creid89/PSU_Capstone_Project_2025_BMS/Schematics/BMS Schematics KiCAD/Battery Management System/untitled.kicad_sch

## KiCad design Schematics/BMS Schematics KiCAD/Battery Management System/untitled.kicad_sch (2025-04-21)

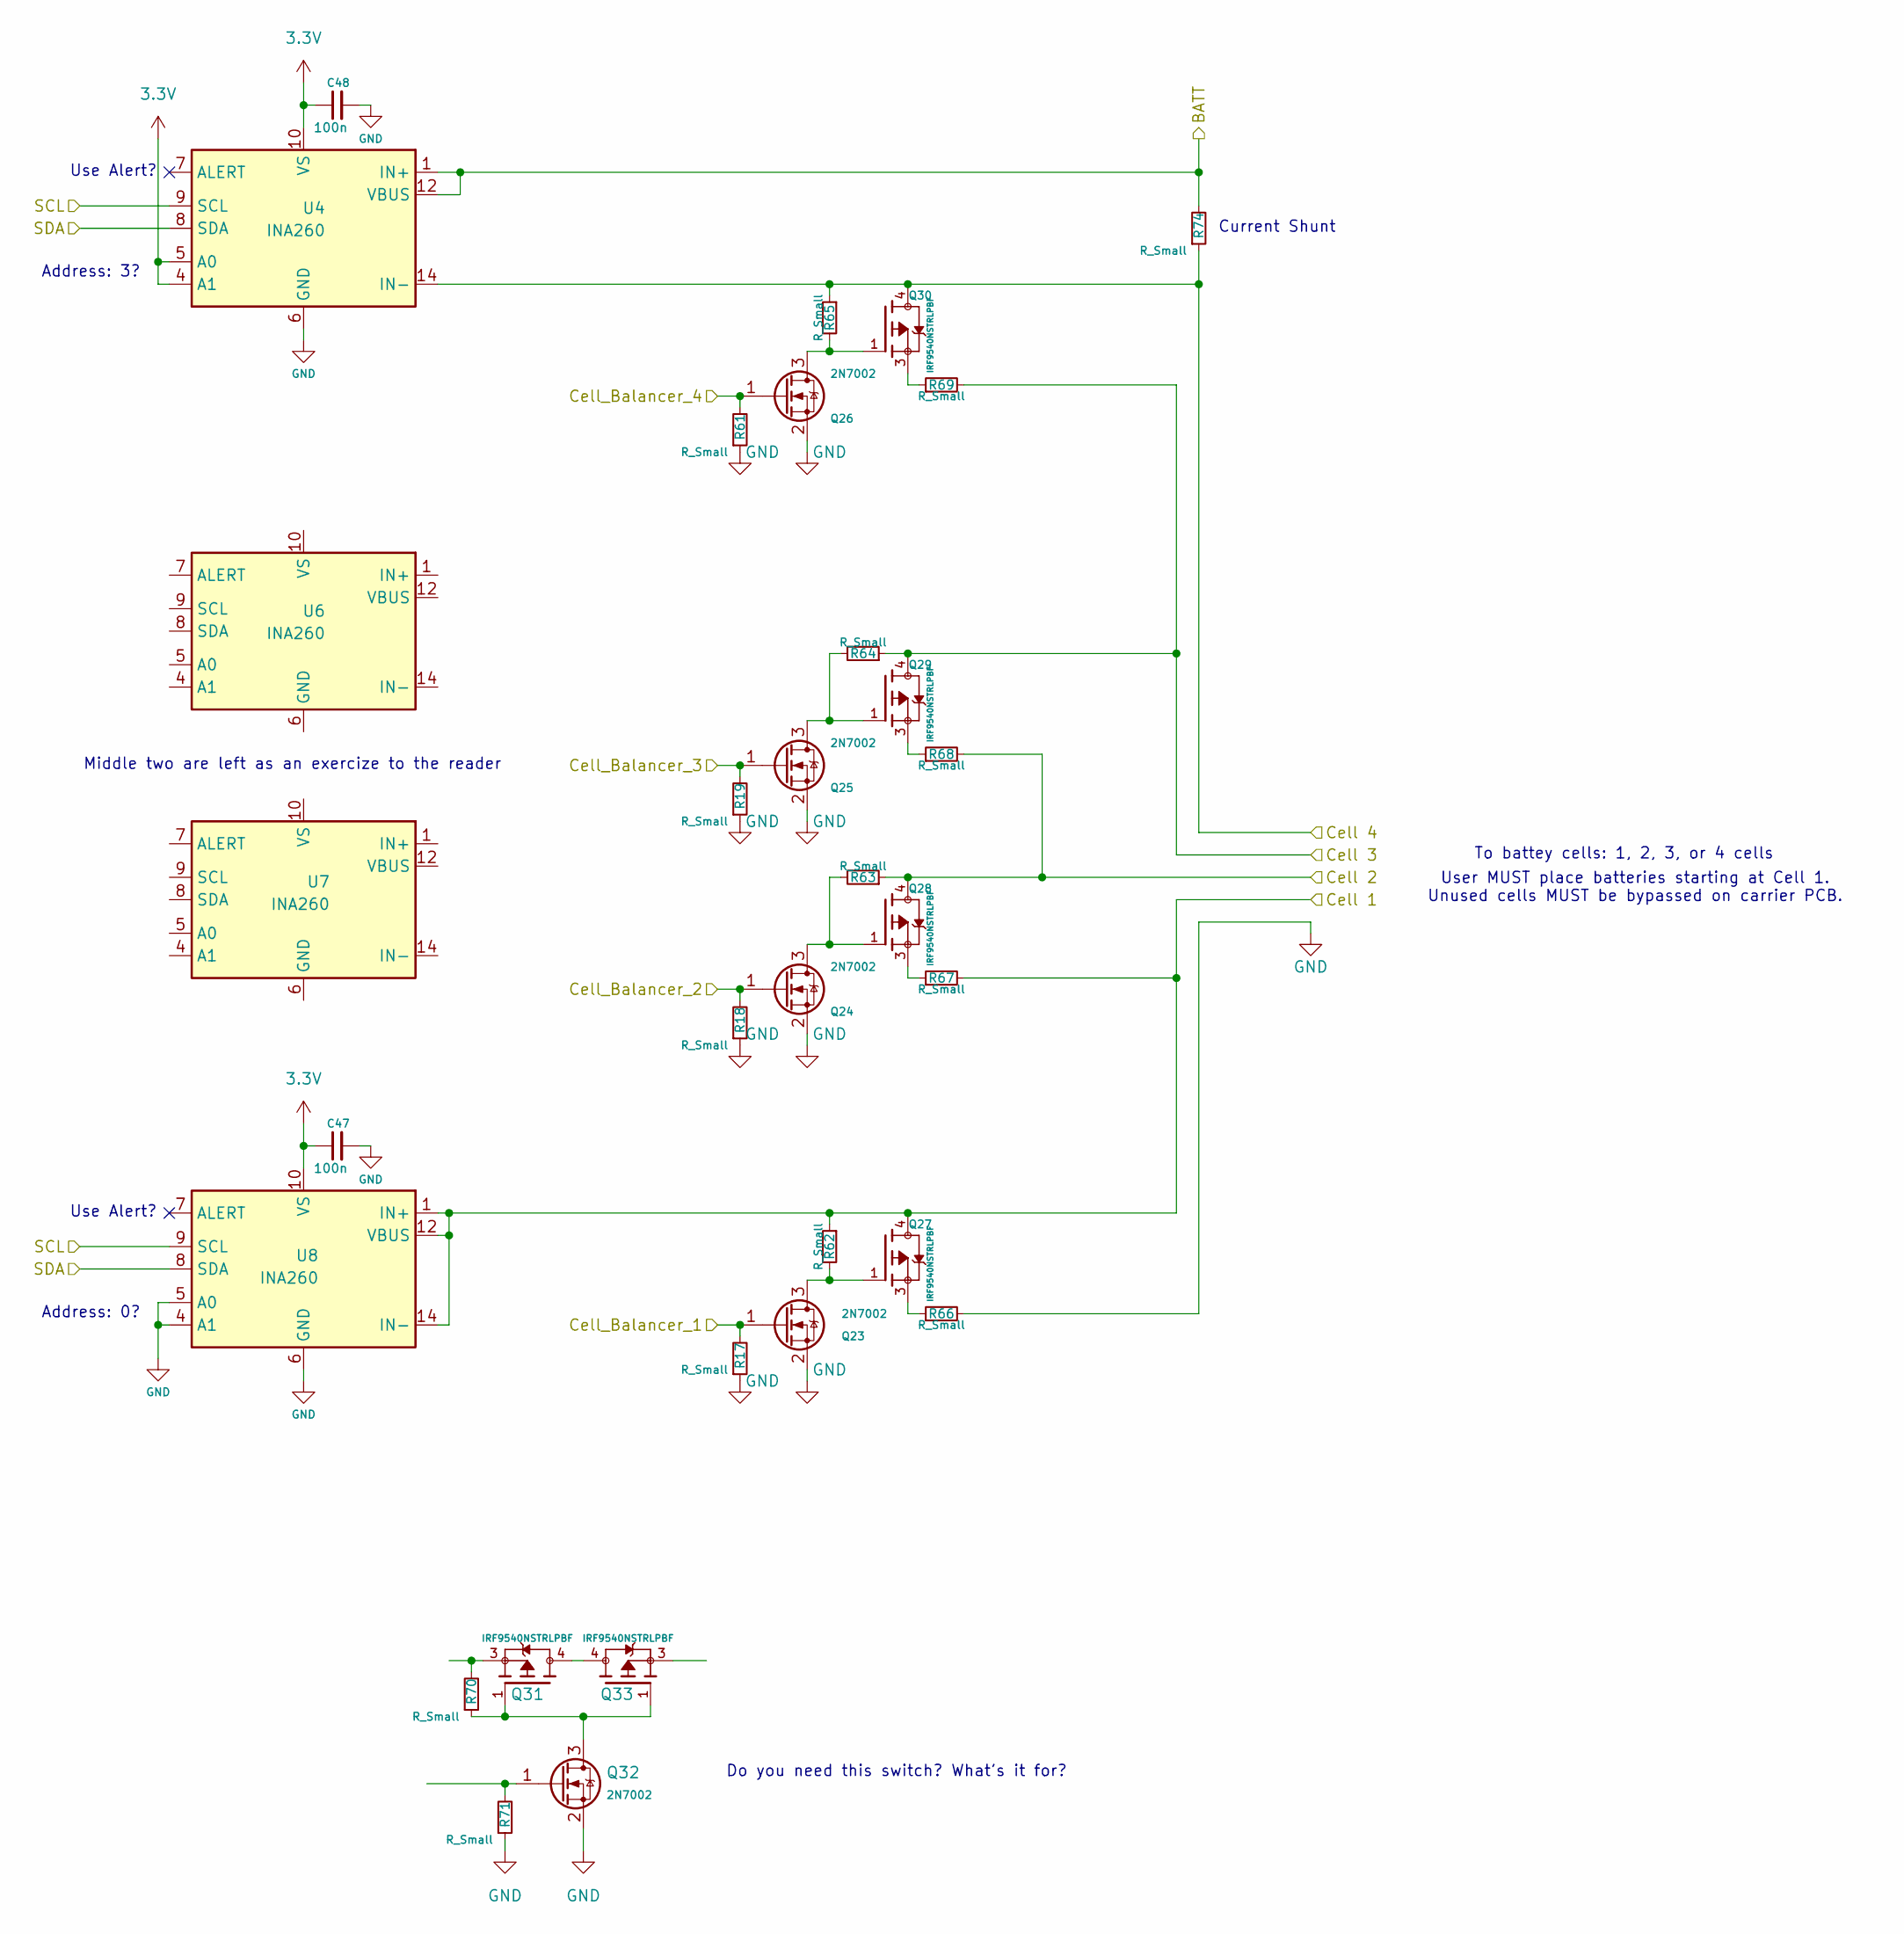
[picture p17: schematic untitled.kicad_sch]

Parts:
C47, C48: 100n; C_0201_0603Metric
Q23, Q24, Q25, Q26, Q32: 2N7002; SOT-23
Q27, Q28, Q29, Q30, Q31, Q33: IRF9540NSTRLPBF; DPAK254P1524X483-4_3N; PARTREV 09/30/05
R17, R18, R19, R61, R71, R74: R_Small; R_0201_0603Metric
R62, R63, R64, R65, R66, R67, R68, R69, R70: R_Small
U4, U6, U7, U8: INA260; TSSOP-16_4.4x5mm_P0.65mm

Connections:
3.3V: C47.1, C48.1, U4.4 (A1), U4.5 (A0), U4.10 (VS), U8.10 (VS)
BATT: R74.2, U4.1 (IN+), U4.12 (VBUS)
Cell 1: Q27.4, R62.1, R67.2, U8.1 (IN+), U8.12 (VBUS), U8.14 (IN-)
Cell 2: Q28.4, R63.1, R68.2
Cell 3: Q29.4, R64.1, R69.2
Cell 4: Q30.4, R65.1, R74.1, U4.14 (IN-)
Cell_Balancer_1: Q23.1 (G), R17.2
Cell_Balancer_2: Q24.1 (G), R18.2
Cell_Balancer_3: Q25.1 (G), R19.2
Cell_Balancer_4: Q26.1 (G), R61.2
GND: C47.2, C48.2, Q23.2 (S), Q24.2 (S), Q25.2 (S), Q26.2 (S), Q32.2 (S), R17.1, R18.1, R19.1, R61.1, R66.2, R71.1, U4.6 (GND), U8.4 (A1), U8.5 (A0), U8.6 (GND)
unnamed: Q23.3 (D), Q27.1, R62.2
unnamed: Q24.3 (D), Q28.1, R63.2
unnamed: Q25.3 (D), Q29.1, R64.2
unnamed: Q26.3 (D), Q30.1, R65.2
unnamed: Q27.3, R66.1
unnamed: Q28.3, R67.1
unnamed: Q29.3, R68.1
unnamed: Q30.3, R69.1
unnamed: Q31.1, Q32.3 (D), Q33.1, R70.1
unnamed: Q31.3, R70.2
unnamed: Q31.4, Q33.4
unnamed: Q32.1 (G), R71.2
SCL: U4.9 (SCL), U8.9 (SCL)
SDA: U4.8 (SDA), U8.8 (SDA)

Notes on the sheet:
Address: 0?
Use Alert?
To battey cells: 1, 2, 3, or 4 cells
Current Shunt
Do you need this switch? What's it for?
Address: 3?
User MUST place batteries starting at Cell 1. Unused cells MUST be bypassed on carrier PCB.
Middle two are left as an exercize to the reader
