creid89/PSU_Capstone_Project_2025_BMS/Code/Arduino Library/examples/ESP32_BMS_Controller_Library_Test_v2/ESP32_BMS_Controller_Library_Test_v2.ino

#include <BMSController.h>

//Using Huzzah Adafruit ESP32
//#define SDA_PIN 23
//#define SCL_PIN 22
#define BMS_ADDR 0x58

BMSController BMS(BMS_ADDR);

void setup() {
  Serial.begin(115200);

  while (!BMS.begin()) {
    Serial.println();
    Serial.println("Waiting for BMS to respond...");
    delay(2000);
  }
  Serial.println("——————————————————————");
  Serial.println("          BMS connected!");
  Serial.println("——————————————————————");
  delay(500);

  BMS.setChargeVoltage(16.8);       // command 0x10
  delay(100);
  BMS.setVsysMin(8.0);              // command 0x11
  delay(100);
  BMS.setInputVoltageLimit(12.5);   // command 0x13
  delay(100);
  BMS.setChargeCurrent(1.5);        // command 0x14
  delay(100);
  BMS.setInputCurrentLimit(3000.0);   // command 0x15
  delay(100);
  BMS.setCellMaxCutOffV(4.0);        // command 0x16
  delay(100);
  BMS.setCellMinCutOffV(2.0);        // command 0x17
  delay(100);
  BMS.setPack_stock_capacity(5200.0);   // command 0x18 

  //BMS.FinishedConfiguration(true);  //command 0x19
  Serial.println("——————————————————————");
  Serial.println("          BMS Configured!");
  Serial.println("——————————————————————");
}

void loop() {
  delay(1500);
  float chargeCurrent = BMS.getChargeCurrent();
  Serial.print("Charge Current: ");
  Serial.println(chargeCurrent, 3);
   delay(1500);
  float cellVoltage1 = BMS.getCell1Voltage();
  Serial.print("Cell 1 Voltage: ");
  Serial.println(cellVoltage1 , 3);
  delay(1500);
  float cellVoltage2 = BMS.getCell2Voltage();
  Serial.print("Cell 2 Voltage: ");
  Serial.println(cellVoltage2 , 3);
  delay(1500);
  float cellVoltage3 = BMS.getCell3Voltage();
  Serial.print("Cell 3 Voltage: ");
  Serial.println(cellVoltage3 , 3);
  delay(1500);
  float cellVoltage4 = BMS.getCell4Voltage();
  Serial.print("Cell 4 Voltage: ");
  Serial.println(cellVoltage4 , 3);
  delay(1500);
  float totalPackVoltage = BMS.getTotalPackVoltage();
  Serial.print("Total Pack Voltage: ");
  Serial.println(totalPackVoltage , 3);
  delay(1500);
  float SoC = BMS.getSoC();
  Serial.print("SoC: ");
  Serial.println(SoC , 3);
  delay(1500);
  float PercentSoC = BMS.getPercentSoC();
  Serial.print("Percent SoC: ");
  Serial.print(PercentSoC , 3);
  Serial.println("%");
}
